BoujeeEnjinia1701/conepro/cad/drawings/CNP-DWG-001.pdf

CONCEPT, NOT FOR FABRICATION | ConePro · github.com/BoujeeEnjinia1701/conepro

FRONT VIEW
Scale 1:20; looking at the front (along +Y)

TOP VIEW
Scale 1:20; looking down (along -Z)

RIGHT VIEW
Scale 1:20; looking at the right side (along -X)

DETAIL A: ANVIL, SENSOR PAD AND CLAMP
Front view, scale 1:5

1,875 overall

713 = 138 + 575 drop

1,000 lower rod

939 stroke (850 usable)

300 plate

300

8 gap, pad to hammer face

105 rod to wire

100 hammer, 8.0 kg

ISOMETRIC VIEW
Not to scale; seen from the front right and above, about 30 deg elevation

MAIN DIMENSIONS AND INTERFACES (MM)
ASTM D6951: 8.0 kg hammer, 575 drop, 16 rod, 20 cone at 60 deg Hammer 100 OD x 22 bore x 138.0; anvil 64 x 60
Upper rod 778; stop collar 44 x 18; T-handle 260 wide
Plate 300 x 300 x 6 Al; 60 hole, 60 slot
Draw-wire exit at X 105, Y 40; 60 grooved drum, single layer
One-piece aluminum clamp, 40 collar against the anvil underside
M12 rod joints, no thread locker; spanner flats 17 A/F cone, 13 A/F rod, 55 A/F anvil Hammer: 3 grip grooves; 33 rubber grips on the T-handle
End cap 32 x 24 on the upper rod stud whenever it is off the anvil
Sensor pad on a band clamp (50 to 80 anvils), 8 below anvil top
Stroke 939, limited by the wire arm on reel housing
About 15.8 kg with bag; heaviest piece 9.96 kg (CNP-CAL-001 v0.6) Third-angle; front view from -Y; ground at Z 0
REV | DESCRIPTION | DATE | BY
P1 | Preliminary GA for TRL 3 (from cad/src/model.py) | 2026-09-25 | AC
P2 | 6 mm plate, aluminum clamp, 15.7 kg (CNP-DDR-002) | 2026-09-25 | AC
P3 | Reel housing 72 x 60 x 72 round the 60 mm drum; stroke 928 (CNP-DDR-003) | 2026-09-27 | AC
P4 | Layout and labels tidied | 2026-09-30 | AC
P5 | Design for construction: joints, clamp, reel, cables (CNP-DDR-004) | 2026-09-30 | AC
P6 | Spanner flats; hammer grooves; grips; end cap (2026-10-02) | 2026-10-02 | AC
CONEPRO | github.com/BoujeeEnjinia1701/conepro

## General arrangement

DRAWING NO.
CNP-DWG-001

REV
P6

SHEET
1 of 1

SIZE

## ANSI B

SCALE
1:20

UNITS
mm
PROJECTION | DATE
2026-10-02

DRAWN
Amish Chadha

MATERIAL / NOTES
Steel rods, anvil, hammer; aluminum plate and clamp; parts per bom/bom.csv. PRELIMINARY, NOT FOR FABRICATION
Licensed CERN-OHL-S-2.0 · Design Molecule Lab · designmolecule.com | Generated from cad/src; do not edit by hand
