BoujeeEnjinia1701/conepro/cad/drawings/CNP-DWG-101.pdf

### BUILD PLAN SKETCH, PLAN NOT YET BUILT ConePro · github.com/BoujeeEnjinia1701/conepro

FRONT VIEW
Scale 2:1; looking at the front (along +Y)

TOP VIEW
Scale 2:1; looking down (along -Z)

RIGHT VIEW
Scale 2:1; looking at the right side (along -X)

20

20 29

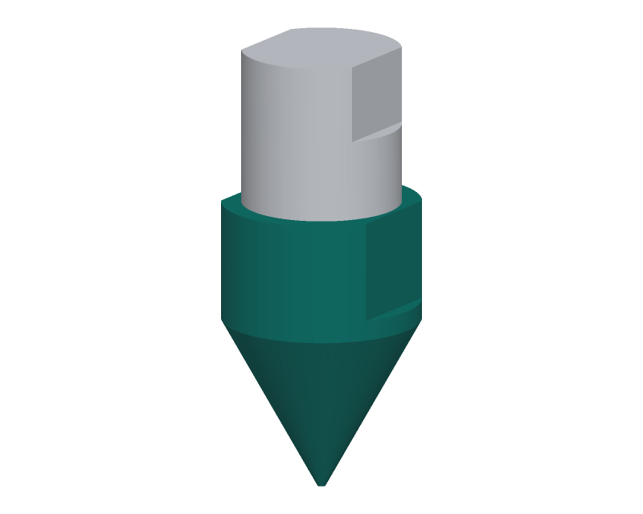
[picture p45: figure]

WHERE IT GOES
This part in colour, its neighbours in grey

HOW TO MAKE IT AND HOW IT FITS
Make two. Turn from 25 mm bar: a 20.0 mm diameter body 12 mm long with a 60 degree point below it (point 17.3 mm high), 29.3 mm overall. Keep the 20 mm diameter within 0.1 mm; a worn or undersize cone biases the DCP index. Leave a sharp point, no flat.
Top face: drill 10.2 mm 16 deep, tap M12 x 1.75 to 14 mm deep, and face it square to the axis: the rod shoulder bears on this face. Spanner flats: mill two flats 17 mm across on the top 10 mm of the body, leaving the bottom 2 mm and the 20 mm base edge round. Harden after tapping (about 50 HRC); run a tap through after. Fit: screws onto the M12 stud on the bottom of the lower rod with no thread locker; tighten with a 17 mm spanner on the cone and a 13 mm spanner on the rod flats until the shoulder seats. Check: 20.0 mm across the body; 60 degrees with a gauge; the rod shoulder sits flat on the top face with no gap.
REV | DESCRIPTION | DATE | BY
P1 | Making sketch for the prototype build plan | 2026-09-30 | AC
P2 | 17 mm spanner flats; no thread locker | 2026-10-02 | AC
CONEPRO | github.com/BoujeeEnjinia1701/conepro

## ConePro cone (make 2, one spare): making sketch

DRAWING NO.
CNP-DWG-101

REV
P2

SHEET
1 of 1

SIZE

## ANSI B

SCALE
2:1

UNITS
mm
PROJECTION | DATE
2026-10-02

DRAWN
Amish Chadha

MATERIAL / NOTES
Tool steel or 4140 round bar 25 mm, hardened after machining
Licensed CERN-OHL-S-2.0 · Design Molecule Lab · designmolecule.com | Generated from cad/src; do not edit by hand
