BoujeeEnjinia1701/conepro/cad/drawings/CNP-DWG-102.pdf

### BUILD PLAN SKETCH, PLAN NOT YET BUILT ConePro · github.com/BoujeeEnjinia1701/conepro

FRONT VIEW
Scale 1:2; looking at the front (along +Y)

TOP VIEW
Scale 1:2; looking down (along -Z)

RIGHT VIEW
Scale 1:2; looking at the right side (along -X)

Broken view: the middle of the rod is left out. True length 1,032 mm overall.

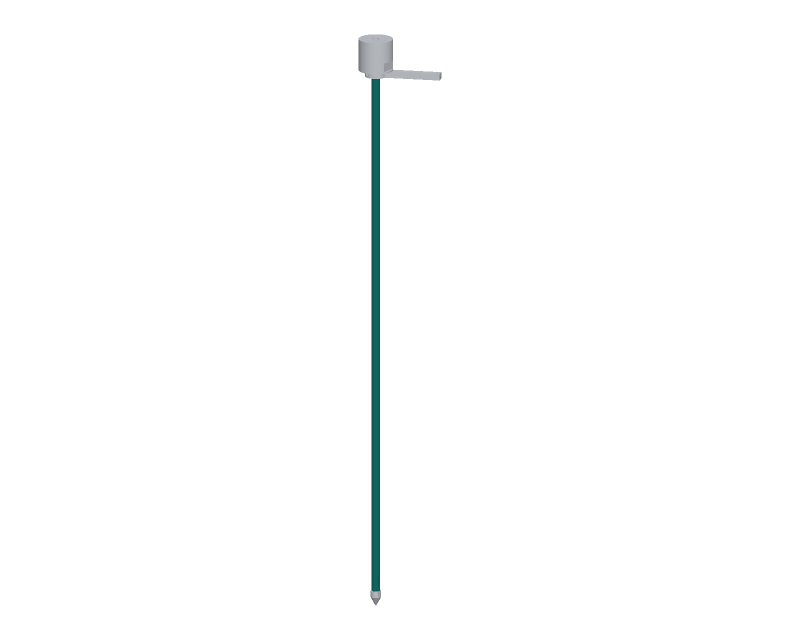
[picture p46: figure]

WHERE IT GOES
This part in colour, its neighbours in grey

HOW TO MAKE IT AND HOW IT FITS
Cut 1,032 mm of 16 mm rod; face both ends square.
Bottom end: turn an M12 x 1.75 stud 12 mm long (12.0 mm diameter) and cut the thread; leave a square, flat 16 mm shoulder.
Top end: turn an M12 stud 20 mm long the same way.
Spanner flats: mill two flats 13 mm across, 20 mm long, starting
8 mm above the bottom shoulder.
The shoulders are 1,000 mm apart. Both shoulders carry every
blow, so face them square and break the edge 0.5 mm.
Engrave a ring every 10 mm, deeper every 100 mm, measured up from the cone point with the cone fitted (the point is 29.3 mm
below the bottom shoulder). This is the backup depth scale.
Fit: the cone screws on the bottom stud, the anvil on the top
stud; the clamp collar slides on from the top before the anvil. Check: straight within 1 mm over its length when rolled on a flat bench; both studs take an M12 nut by hand.
REV | DESCRIPTION | DATE | BY
P1 | Making sketch for the prototype build plan | 2026-09-30 | AC
P2 | 13 mm spanner flats near the bottom shoulder | 2026-10-02 | AC
CONEPRO | github.com/BoujeeEnjinia1701/conepro

## ConePro lower drive rod: making sketch

DRAWING NO.
CNP-DWG-102

REV
P2

SHEET
1 of 1

SIZE

## ANSI B

SCALE
1:2

UNITS
mm
PROJECTION | DATE
2026-10-02

DRAWN
Amish Chadha

MATERIAL / NOTES
16 mm 4140 class steel rod, ground or bright
Licensed CERN-OHL-S-2.0 · Design Molecule Lab · designmolecule.com | Generated from cad/src; do not edit by hand
