BoujeeEnjinia1701/conepro/cad/drawings/CNP-DWG-103.pdf

### BUILD PLAN SKETCH, PLAN NOT YET BUILT ConePro · github.com/BoujeeEnjinia1701/conepro

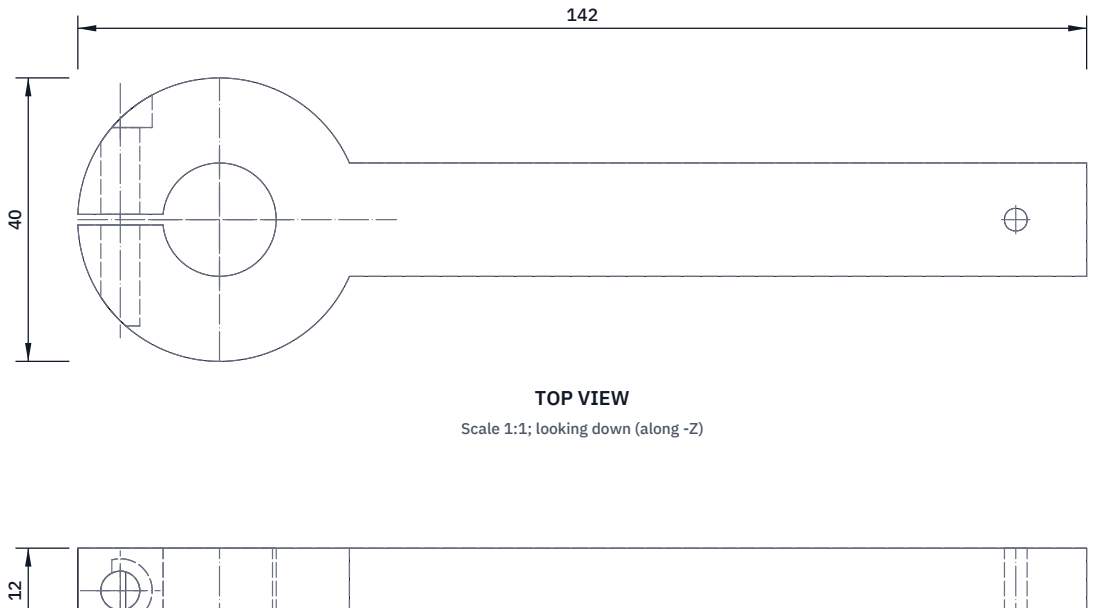
[picture p47: figure]
TOP VIEW; Scale 1:1; looking down (along -Z)

FRONT VIEW
Scale 1:1; looking at the front (along +Y)

RIGHT VIEW
Scale 1:1; looking at the right side (along -X)

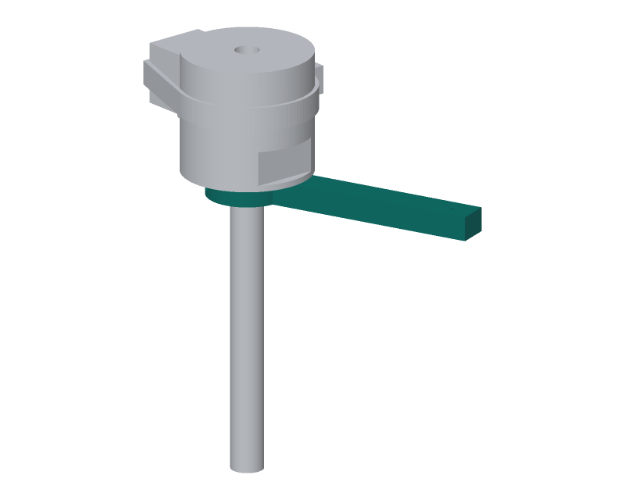
[picture p48: figure]

WHERE IT GOES
This part in colour, its neighbours in grey

HOW TO MAKE IT AND HOW IT FITS
One piece cut from 12 mm plate: a 40 mm round boss and an arm 16 mm wide reaching 122 mm from the boss centre.
Bore the boss 16 mm (a sliding fit on the rod, ream if you can). Wire eye: a 3.2 mm hole on the arm centre line, 112.4 mm from the bore centre; break both edges so the wire cannot chafe.
Saw a 1.5 mm slit from the bore out through the boss on the side opposite the arm.
Clamp screw: at 14 mm from the bore centre, square across the slit, drill 5.5 mm through the near jaw with a 9 mm spot face, and
drill 4.2 mm and tap M5 in the far jaw.
Fit: slides on the lower rod from the top; its top face butts the underside of the anvil, which carries it at every blow. Turn the arm to point at the reel's wire exit, then tighten the M5 screw. Check: slides on the rod with the screw slack; locks by hand.
REV | DESCRIPTION | DATE | BY
P1 | Making sketch for the prototype build plan | 2026-09-30 | AC
CONEPRO | github.com/BoujeeEnjinia1701/conepro

## ConePro clamp collar and wire arm: making sketch

DRAWING NO.
CNP-DWG-103

REV
P1

SHEET
1 of 1

SIZE

## ANSI B

SCALE
1:1

UNITS
mm
PROJECTION | DATE
2026-09-30

DRAWN
Amish Chadha

MATERIAL / NOTES
Aluminium plate 12 mm, 6061 class
Licensed CERN-OHL-S-2.0 · Design Molecule Lab · designmolecule.com | Generated from cad/src; do not edit by hand
