BoujeeEnjinia1701/conepro/cad/drawings/CNP-DWG-104.pdf

### BUILD PLAN SKETCH, PLAN NOT YET BUILT ConePro · github.com/BoujeeEnjinia1701/conepro

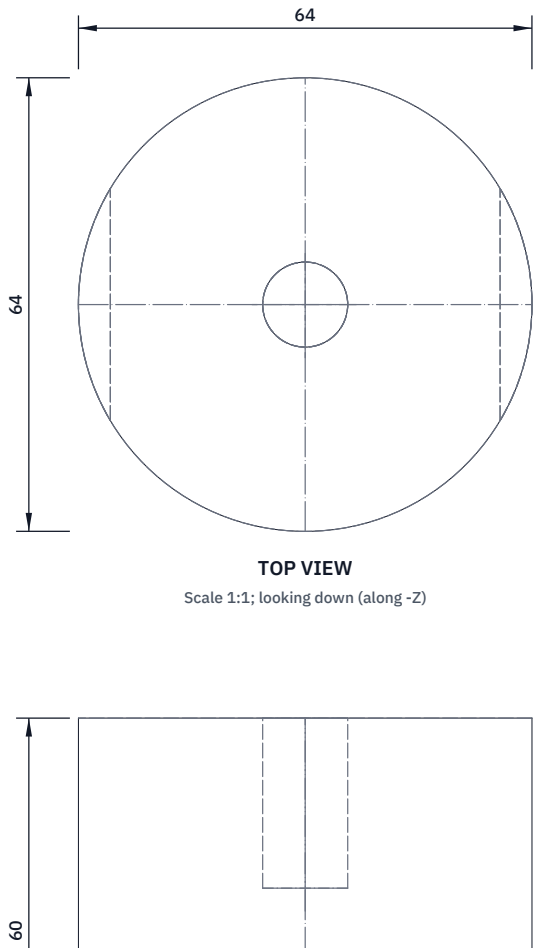
[picture p49: figure]
TOP VIEW; Scale 1:1; looking down (along -Z)

FRONT VIEW
Scale 1:1; looking at the front (along +Y)

RIGHT VIEW
Scale 1:1; looking at the right side (along -X)

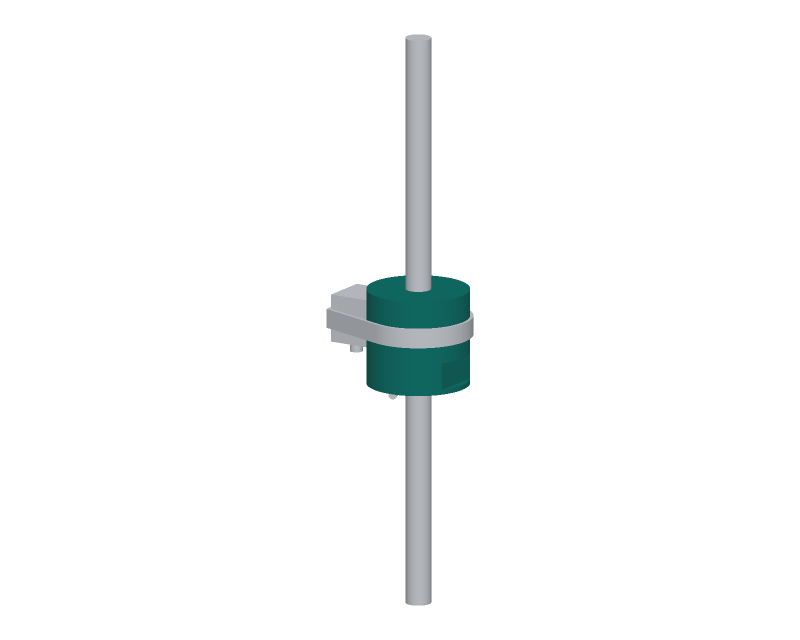
[picture p50: figure]

WHERE IT GOES
This part in colour, its neighbours in grey

HOW TO MAKE IT AND HOW IT FITS
Turn to 64 mm diameter x 60 mm long; face both ends square and parallel within 0.1 mm. Chamfer the outer edges 1 mm.
Both end faces: centre drill, drill 10.2 mm 27 mm deep and tap M12 x 1.75 to 24 mm deep. The two holes do not meet.
Spanner flats: mill two flats 55 mm across, 17 mm long, starting 3 mm above the bottom face, below the sensor pad.
The top face takes every hammer blow: leave it flat and smooth. Fit: both rod studs screw in to their shoulders with no thread locker, tightened with a 55 mm spanner on the anvil and the rod flats or T-handle. The clamp collar butts the bottom face; the sensor pad and band clamp onto its side.
Check: both rods seat on their shoulders with no rock; the anvil spins true on the rod within 0.2 mm.
REV | DESCRIPTION | DATE | BY
P1 | Making sketch for the prototype build plan | 2026-09-30 | AC
P2 | 55 mm spanner flats; no thread locker | 2026-10-02 | AC
CONEPRO | github.com/BoujeeEnjinia1701/conepro

## ConePro anvil: making sketch

DRAWING NO.
CNP-DWG-104

REV
P2

SHEET
1 of 1

SIZE

## ANSI B

SCALE
1:1

UNITS
mm
PROJECTION | DATE
2026-10-02

DRAWN
Amish Chadha

MATERIAL / NOTES
Steel round bar 70 mm, 1045 or 4140 class
Licensed CERN-OHL-S-2.0 · Design Molecule Lab · designmolecule.com | Generated from cad/src; do not edit by hand
