BoujeeEnjinia1701/conepro/cad/drawings/CNP-DWG-105.pdf

### BUILD PLAN SKETCH, PLAN NOT YET BUILT ConePro · github.com/BoujeeEnjinia1701/conepro

FRONT VIEW
Scale 1:2; looking at the front (along +Y)

TOP VIEW
Scale 1:2; looking down (along -Z)

RIGHT VIEW
Scale 1:2; looking at the right side (along -X)

100

100 138

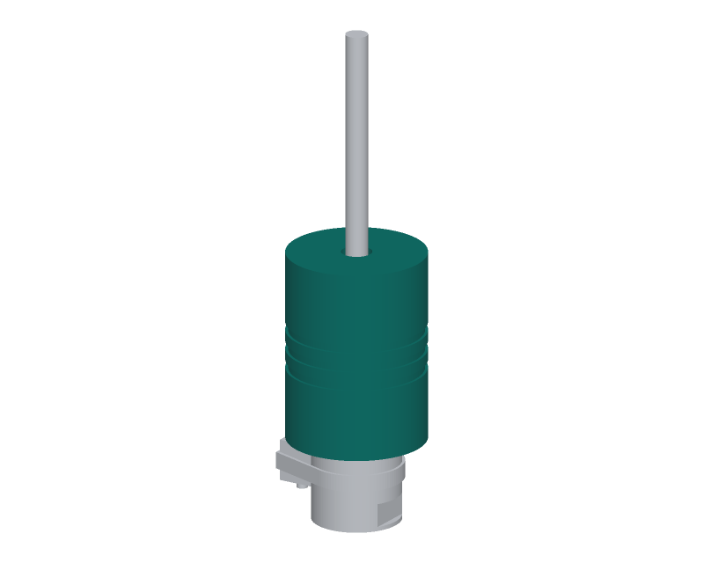
[picture p51: figure]

WHERE IT GOES
This part in colour, its neighbours in grey

HOW TO MAKE IT AND HOW IT FITS
Saw 140 mm of 100 mm bar. Bore 22 mm through.
Face both ends square; the lower face strikes the anvil.
Lower face: 16 pockets 8.2 mm diameter, 5 mm deep, equally spaced (22.5 degrees) on an 82 mm circle, all outside the 64 mm area
that strikes the anvil.
Grip grooves: turn 3 grooves 6 mm wide and 2 mm deep,
14 mm apart, centred on the middle of the length.
Weigh, then face the top end down to 8.00 kg, within 10 g.
The length is set at machining (about 138.0 mm).
Bond a 8 x 4 mm N42 magnet in each pocket with epoxy, 0.5 mm below the face, every one with the same pole facing down. Paint or oil the outside; keep the strike face bare. Stick the
"fit the end cap" label above the grooves.
Fit: slides on the upper rod (3 mm clearance all round) and falls 575 mm onto the anvil.
Check: 8.00 kg; slides freely the length of a 16 mm rod; no magnet stands proud of the face.
REV | DESCRIPTION | DATE | BY
P1 | Making sketch for the prototype build plan | 2026-09-30 | AC
P2 | Grip grooves; length set to keep 8.00 kg; label | 2026-10-02 | AC
CONEPRO | github.com/BoujeeEnjinia1701/conepro

## ConePro drop hammer: making sketch

DRAWING NO.
CNP-DWG-105

REV
P2

SHEET
1 of 1

SIZE

## ANSI B

SCALE
1:2

UNITS
mm
PROJECTION | DATE
2026-10-02

DRAWN
Amish Chadha

MATERIAL / NOTES
Steel round bar 100 mm, 1018 to 1045 class
Licensed CERN-OHL-S-2.0 · Design Molecule Lab · designmolecule.com | Generated from cad/src; do not edit by hand
