BoujeeEnjinia1701/conepro/cad/drawings/CNP-DWG-106.pdf

### BUILD PLAN SKETCH, PLAN NOT YET BUILT ConePro · github.com/BoujeeEnjinia1701/conepro

FRONT VIEW
Scale 1:2; looking at the front (along +Y)

TOP VIEW
Scale 1:2; looking down (along -Z)

RIGHT VIEW
Scale 1:2; looking at the right side (along -X)

Broken view: the middle of the rod is left out. True length 798 mm overall.

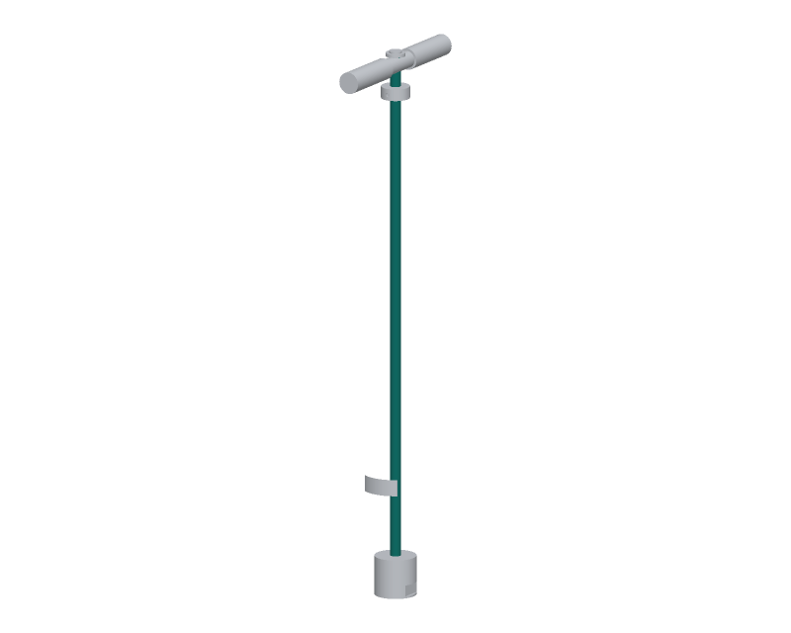
[picture p52: figure]

WHERE IT GOES
This part in colour, its neighbours in grey

HOW TO MAKE IT AND HOW IT FITS
Cut 798 mm of 16 mm rod; face both ends square.
Bottom end: turn an M12 x 1.75 stud 20 mm long with a square shoulder. The shoulder is the anvil top: measure from it.
The rod above the shoulder is 778.0 mm; its top end ends flush with the top of the T-handle tube.
Smooth the rod between the shoulder and 715 mm: the hammer slides on it.
The 6 mm roll pin hole, 722.0 mm above the shoulder, is drilled through the rod and the stop collar together (DWG-107).
Fit: the hammer goes on from the bottom end and the end cap screws on the stud; take it off to screw the stud into the
anvil with no thread locker, turned by the T-handle.
Check: straight within 0.5 mm; the hammer slides its whole length without sticking.
REV | DESCRIPTION | DATE | BY
P1 | Making sketch for the prototype build plan | 2026-09-30 | AC
P2 | Lengths for the grooved hammer; end cap; no thread locker | 2026-10-02 | AC
CONEPRO | github.com/BoujeeEnjinia1701/conepro

## ConePro upper rod (hammer guide): making sketch

DRAWING NO.
CNP-DWG-106

REV
P2

SHEET
1 of 1

SIZE

## ANSI B

SCALE
1:2

UNITS
mm
PROJECTION | DATE
2026-10-02

DRAWN
Amish Chadha

MATERIAL / NOTES
16 mm 4140 class steel rod, ground or bright
Licensed CERN-OHL-S-2.0 · Design Molecule Lab · designmolecule.com | Generated from cad/src; do not edit by hand
