BoujeeEnjinia1701/conepro/cad/drawings/CNP-DWG-107.pdf

### BUILD PLAN SKETCH, PLAN NOT YET BUILT ConePro · github.com/BoujeeEnjinia1701/conepro

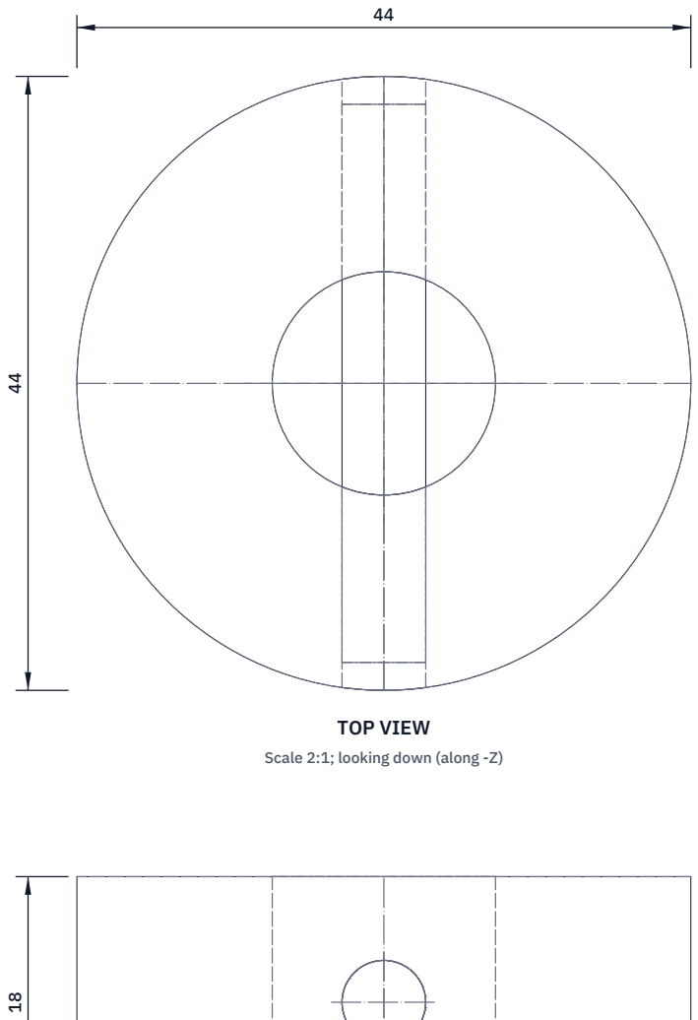
[picture p53: figure]
TOP VIEW; Scale 2:1; looking down (along -Z)

FRONT VIEW
Scale 2:1; looking at the front (along +Y)

RIGHT VIEW
Scale 2:1; looking at the right side (along -X)

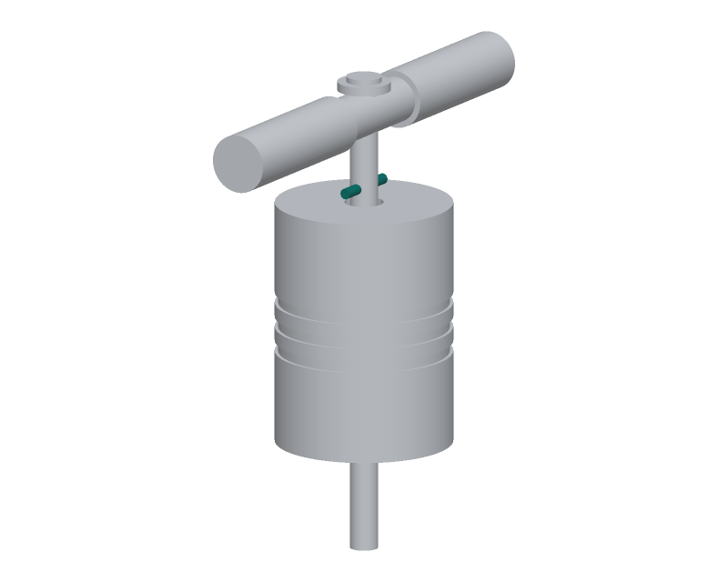
[picture p54: figure]

WHERE IT GOES
This part in colour, its neighbours in grey

HOW TO MAKE IT AND HOW IT FITS
Turn to 44 mm diameter x 18 mm; bore 16 mm, a close slide fit. Face both ends square; the hammer's top face hits the underside. Slide it on the upper rod from the top so its underside is
713.0 mm above the rod shoulder. With the 138.0 mm hammer this gives the 575 mm free drop. Set it with a rule and check
the drop with the hammer on a flat plate standing for the anvil. Clamp it there and drill 6 mm straight through collar and rod together, at mid-height (722.0 mm above the shoulder).
Drive in a 6 x 40 mm spring steel roll pin; its ends sit just
inside the collar's outside surface.
Check: the free drop is 575 mm, within 2 mm; the collar does not move when the hammer is jerked up against it.
REV | DESCRIPTION | DATE | BY
P1 | Making sketch for the prototype build plan | 2026-09-30 | AC
P2 | Heights for the grooved hammer | 2026-10-02 | AC
CONEPRO | github.com/BoujeeEnjinia1701/conepro

## ConePro top stop collar: making sketch

DRAWING NO.
CNP-DWG-107

REV
P2

SHEET
1 of 1

SIZE

## ANSI B

SCALE
2:1

UNITS
mm
PROJECTION | DATE
2026-10-02

DRAWN
Amish Chadha

MATERIAL / NOTES
Steel round bar 50 mm, 1018 class
Licensed CERN-OHL-S-2.0 · Design Molecule Lab · designmolecule.com | Generated from cad/src; do not edit by hand
