BoujeeEnjinia1701/conepro/cad/drawings/CNP-DWG-108.pdf

### BUILD PLAN SKETCH, PLAN NOT YET BUILT ConePro · github.com/BoujeeEnjinia1701/conepro

FRONT VIEW
Scale 1:2; looking at the front (along +Y)

TOP VIEW
Scale 1:2; looking down (along -Z)

RIGHT VIEW
Scale 1:2; looking at the right side (along -X)

266

33 38

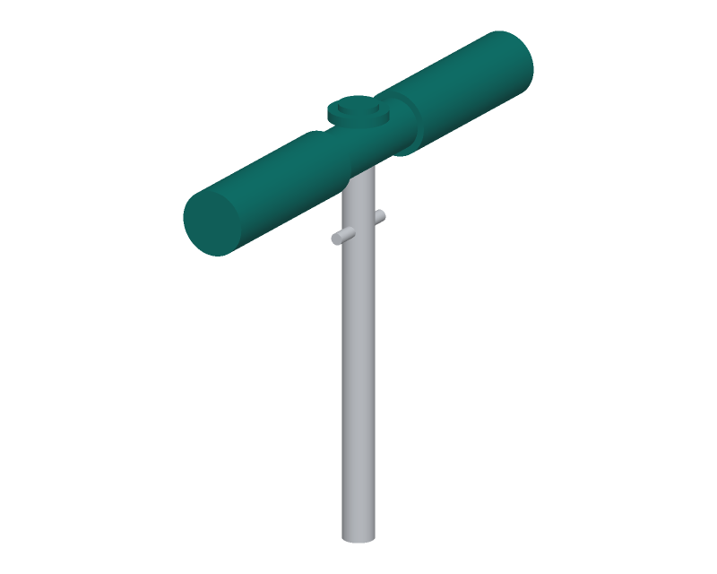
[picture p55: figure]

WHERE IT GOES
This part in colour, its neighbours in grey

HOW TO MAKE IT AND HOW IT FITS
Tube: cut 260 mm of 26 x 2.5 mm steel tube; deburr.
At mid-length drill 16 mm straight through both walls, square to the tube, so the upper rod passes through.
Seat disc: 30 mm diameter, 5 mm thick, with a 20 mm recess 3 mm deep in its top face.
Fit: push the upper rod up through the tube until its top end is flush with the top of the tube, the tube square to the rod.
Weld the tube to the rod all round where the rod comes out, top and bottom (or have a shop do it). Weld the disc centred on the rod top. Paint, then bond the 20 mm bubble level in the recess. Grips: push a closed-end rubber grip, about 33 mm across and 100 mm long, over each tube end (soapy water helps).
Check: the level reads centred when the rod hangs plumb; the handle is square to the rod within 1 degree.
REV | DESCRIPTION | DATE | BY
P1 | Making sketch for the prototype build plan | 2026-09-30 | AC
P2 | Rubber grips on the tube ends | 2026-10-02 | AC
CONEPRO | github.com/BoujeeEnjinia1701/conepro

## ConePro T-handle, level seat and level: making sketch

DRAWING NO.
CNP-DWG-108

REV
P2

SHEET
1 of 1

SIZE

## ANSI B

SCALE
1:2

UNITS
mm
PROJECTION | DATE
2026-10-02

DRAWN
Amish Chadha

MATERIAL / NOTES
Steel tube 26 x 2.5 mm; steel disc 30 x 5 mm; bought bullseye level
Licensed CERN-OHL-S-2.0 · Design Molecule Lab · designmolecule.com | Generated from cad/src; do not edit by hand
