BoujeeEnjinia1701/conepro/cad/drawings/CNP-DWG-109.pdf

### BUILD PLAN SKETCH, PLAN NOT YET BUILT ConePro · github.com/BoujeeEnjinia1701/conepro

FRONT VIEW
Scale 1:1; looking at the front (along +Y)

TOP VIEW
Scale 1:1; looking down (along -Z)

RIGHT VIEW
Scale 1:1; looking at the right side (along -X)

21

30 38

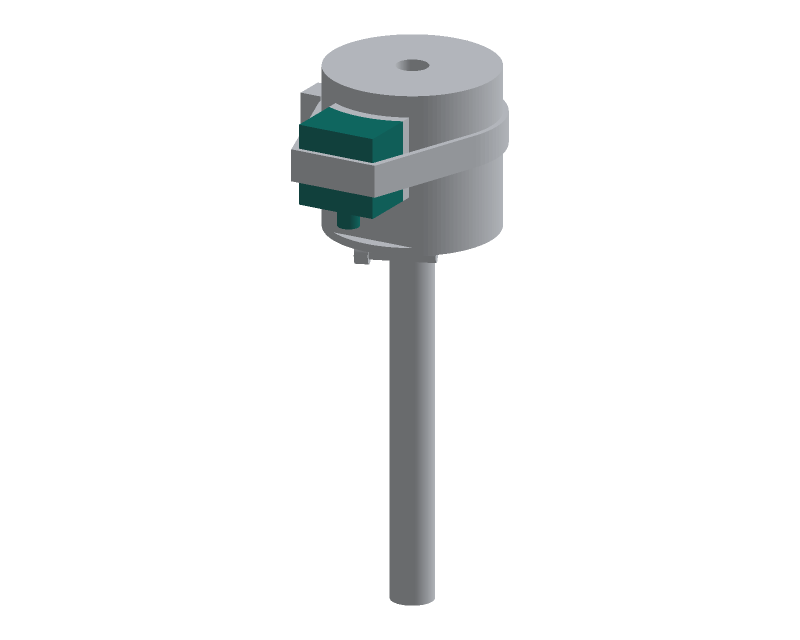
[picture p56: figure]

WHERE IT GOES
This part in colour, its neighbours in grey

HOW TO MAKE IT AND HOW IT FITS
Shell: print 30 wide x 30 tall x 18 deep at the middle, open at the back, 2 mm walls. The face toward the anvil is curved to a 36 mm radius (anvil radius plus the 4 mm isolator).
For another anvil size use its radius plus 4 mm.
Fit the sensor board (Hall switch and accelerometer) with the Hall switch 1 mm under the top face; feed the cable through the 6 mm hole in the boss under the pad.
Fill with potting epoxy; let it cure fully before use.
Isolator: cut 30 x 30 mm of 4 mm elastomer; it bends to the anvil. Bond it to the pad's curved face.
Fit: the pad sits on the anvil side, its top 8 mm below the anvil top, under the hammer's overhang. The band clamp goes round the anvil and over the pad's outer face.
Check: the pad is fully potted; no wire shows at the top.
REV | DESCRIPTION | DATE | BY
P1 | Making sketch for the prototype build plan | 2026-09-30 | AC
CONEPRO | github.com/BoujeeEnjinia1701/conepro

## ConePro blow and tilt sensor pad: making sketch

DRAWING NO.
CNP-DWG-109

REV
P1

SHEET
1 of 1

SIZE

## ANSI B

SCALE
1:1

UNITS
mm
PROJECTION | DATE
2026-09-30

DRAWN
Amish Chadha

MATERIAL / NOTES
Printed PETG or ASA shell, potting epoxy; 4 mm elastomer sheet
Licensed CERN-OHL-S-2.0 · Design Molecule Lab · designmolecule.com | Generated from cad/src; do not edit by hand
