BoujeeEnjinia1701/conepro/cad/drawings/CNP-DWG-110.pdf

### BUILD PLAN SKETCH, PLAN NOT YET BUILT ConePro · github.com/BoujeeEnjinia1701/conepro

FRONT VIEW
Scale 1:5; looking at the front (along +Y)

TOP VIEW
Scale 1:5; looking down (along -Z)

RIGHT VIEW
Scale 1:5; looking at the right side (along -X)

300

300 6

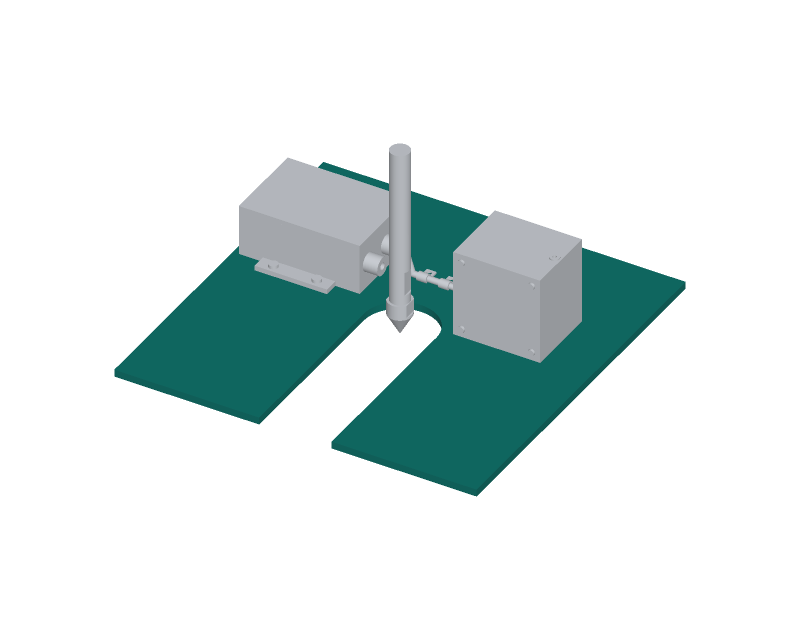
[picture p57: figure]

WHERE IT GOES
This part in colour, its neighbours in grey

HOW TO MAKE IT AND HOW IT FITS
Cut a 300 x 300 mm blank; round the corners 10 mm; deburr. Positions from the plate centre: X toward the reel side, Y away from the slot. The hole positions picture repeats them.
Centre hole 60 mm; a 60 mm wide slot from the hole to the -Y edge (chain drill, jigsaw, file straight).
Reel: four 4.2 mm holes, countersunk from below for M4, at X 45.3 and 103.3, Y 30 and 60.
Logger flanges: four holes drilled 3.3 mm and tapped M4 at X -113 and -77, Y 14 and 96.
P-clips: two holes tapped M4 at (X 4, Y 66) and (X -14, Y 66). Check: lies flat on a bench within 1 mm; screw heads under the plate sit flush or below the bottom face.
REV | DESCRIPTION | DATE | BY
P1 | Making sketch for the prototype build plan | 2026-09-30 | AC
CONEPRO | github.com/BoujeeEnjinia1701/conepro

## ConePro reference plate: making sketch

DRAWING NO.
CNP-DWG-110

REV
P1

SHEET
1 of 1

SIZE

## ANSI B

SCALE
1:5

UNITS
mm
PROJECTION | DATE
2026-09-30

DRAWN
Amish Chadha

MATERIAL / NOTES
Aluminium plate 6 mm, 5083 or 6082 class
Licensed CERN-OHL-S-2.0 · Design Molecule Lab · designmolecule.com | Generated from cad/src; do not edit by hand
