BoujeeEnjinia1701/conepro/cad/drawings/CNP-DWG-111.pdf

### BUILD PLAN SKETCH, PLAN NOT YET BUILT ConePro · github.com/BoujeeEnjinia1701/conepro

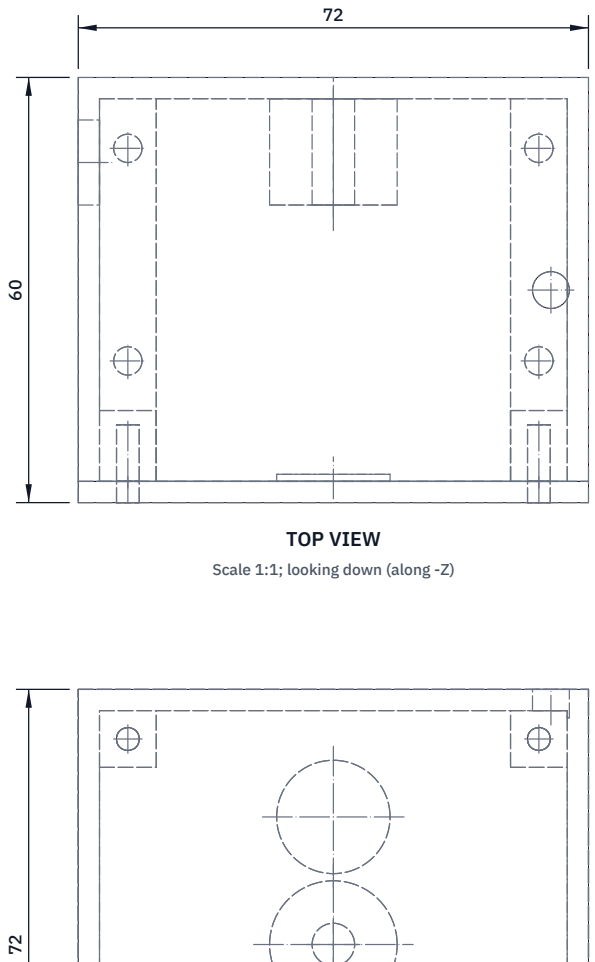
[picture p58: figure]
TOP VIEW; Scale 1:1; looking down (along -Z)
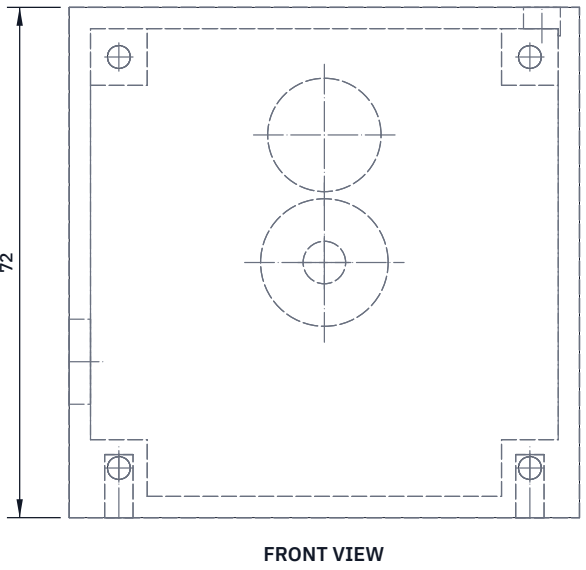
[picture p59: figure]
FRONT VIEW

Scale 1:1; looking at the front (along +Y)

RIGHT VIEW
Scale 1:1; looking at the right side (along -X)

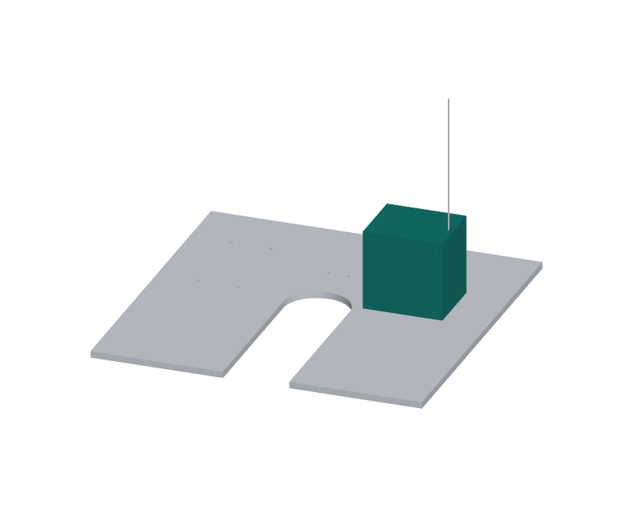
[picture p60: figure]

WHERE IT GOES
This part in colour, its neighbours in grey

HOW TO MAKE IT AND HOW IT FITS
Body: 72 wide x 57 deep x 72 tall outside, 3 mm walls, open on the front (-Y) face. Print standing on its base.
Inside, four 8 x 8 mm posts at the corners: the lower two run front to back, the upper two are 10 mm long at the front.
Bearing boss on the back wall, 18 mm diameter x 15 mm, centred 36 mm from the left face and 36 mm up: press in two 6 x 13 x 5 mm bearings.
Top: a 5.2 mm hole for the wire eyelet, 5.3 mm in from the right face and on the front-to-back centre line.
Left face: a 12 mm hole for the cable gland, 12 mm from the back and 22 mm up.
Inserts: M4 into the lower posts from below (two per post, 20 and 50 mm from the front); M3 into the four post ends at the front. Lid: 72 x 72 x 3 mm, four 3.4 mm holes over the post ends, and a pad for the sensor board. Seal with a 1.5 mm cord in the joint.
REV | DESCRIPTION | DATE | BY
P1 | Making sketch for the prototype build plan | 2026-09-30 | AC
CONEPRO | github.com/BoujeeEnjinia1701/conepro

## ConePro draw-wire reel housing and lid: making sketch

DRAWING NO.
CNP-DWG-111

REV
P1

SHEET
1 of 1

SIZE

## ANSI B

SCALE
1:1

UNITS
mm
PROJECTION | DATE
2026-09-30

DRAWN
Amish Chadha

MATERIAL / NOTES
Printed ASA or PETG, 100 % infill walls; brass heat-set inserts
Licensed CERN-OHL-S-2.0 · Design Molecule Lab · designmolecule.com | Generated from cad/src; do not edit by hand
