BoujeeEnjinia1701/conepro/cad/drawings/CNP-DWG-112.pdf

### BUILD PLAN SKETCH, PLAN NOT YET BUILT ConePro · github.com/BoujeeEnjinia1701/conepro

FRONT VIEW
Scale 1:1; looking at the front (along +Y)

TOP VIEW
Scale 1:1; looking down (along -Z)

RIGHT VIEW
Scale 1:1; looking at the right side (along -X)

60

20 60

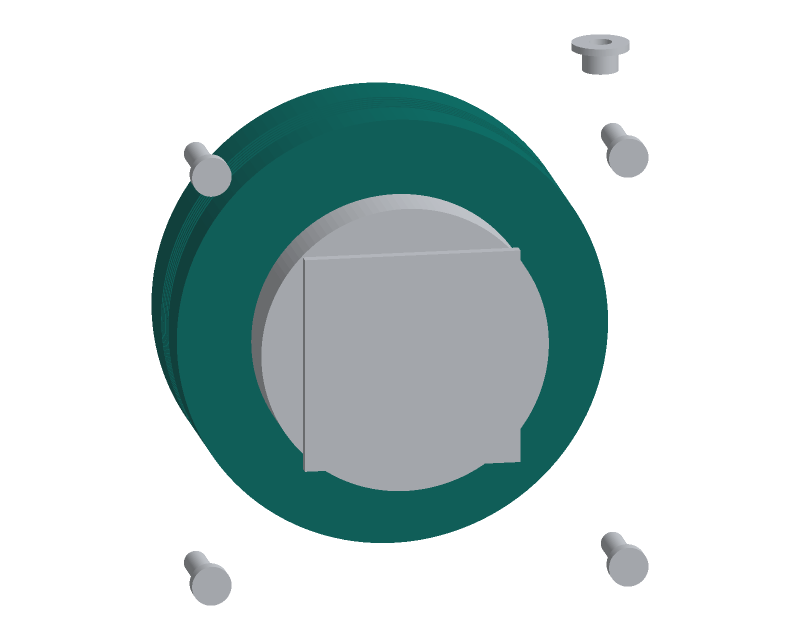
[picture p61: figure]

WHERE IT GOES
This part in colour, its neighbours in grey

HOW TO MAKE IT AND HOW IT FITS
Turn to 60.0 mm diameter x 20 mm; bore 6 mm (a close fit on the shaft). The diameter sets the scale: 188.5 mm of wire per turn. Cut a helical groove 1 mm pitch and 0.5 mm deep over 7 mm of the width, centred, with the lathe set to screw-cut 1 mm pitch. Drill a 1 mm anchor hole at the start of the groove for the
wire end, and an M3 set screw hole into the bore.
Fit: on the 6 mm shaft beside the spring motor, set screw on the shaft flat. The wire leaves the drum straight up under the eyelet: the drum's right-hand edge is under the eyelet. Wind the 1,000 mm wire on in a single layer, in the groove. Check: runs true within 0.05 mm; the wire lies in the groove in one layer with the arm at the full 939 mm stroke.
REV | DESCRIPTION | DATE | BY
P1 | Making sketch for the prototype build plan | 2026-09-30 | AC
CONEPRO | github.com/BoujeeEnjinia1701/conepro

## ConePro draw-wire drum: making sketch

DRAWING NO.
CNP-DWG-112

REV
P1

SHEET
1 of 1

SIZE

## ANSI B

SCALE
1:1

UNITS
mm
PROJECTION | DATE
2026-09-30

DRAWN
Amish Chadha

MATERIAL / NOTES
Aluminium round bar 65 mm, 6061 class
Licensed CERN-OHL-S-2.0 · Design Molecule Lab · designmolecule.com | Generated from cad/src; do not edit by hand
