BoujeeEnjinia1701/conepro/cad/drawings/CNP-DWG-113.pdf

### BUILD PLAN SKETCH, PLAN NOT YET BUILT ConePro · github.com/BoujeeEnjinia1701/conepro

FRONT VIEW
Scale 1:2; looking at the front (along +Y)

TOP VIEW
Scale 1:2; looking down (along -Z)

RIGHT VIEW
Scale 1:2; looking at the right side (along -X)

100

94 42

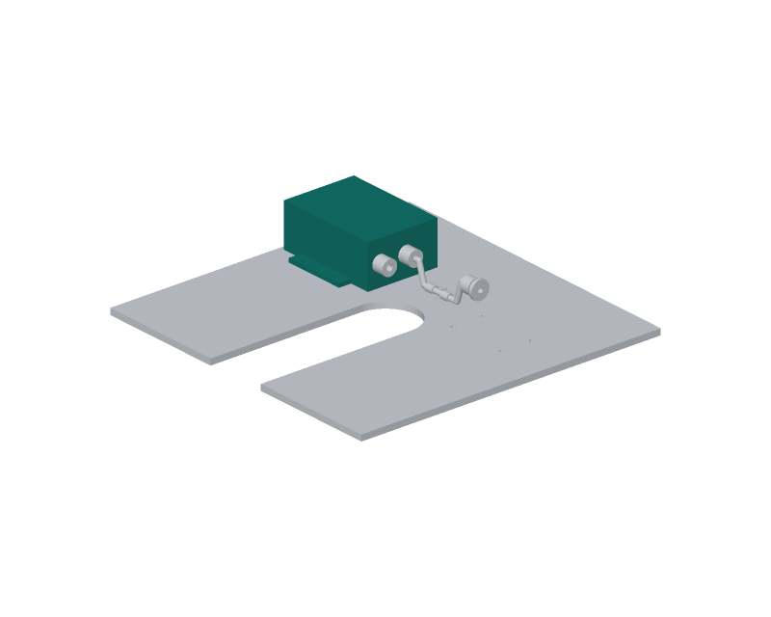
[picture p62: figure]

WHERE IT GOES
This part in colour, its neighbours in grey

HOW TO MAKE IT AND HOW IT FITS
Buy a flanged IP65 box about 100 x 70 x 42 mm with a gasketed lid; its flange holes go 82 mm apart across the box and 36 mm apart along it (or move the plate holes to suit your box).
Drill two 12 mm holes in the end wall that faces the rod, both
21 mm above the box floor's underside: one 12 mm and one 38 mm from the box side nearest the plate slot.
The first takes the M12 gland for the coiled sensor cable, the second the gland for the reel cable.
Pilot drill 3 mm, open with a step drill at low speed, deburr. Inside: the three-AA holder on the floor at the far end, the logger board near the glands, on double-sided foam tape or the box's own bosses.
Fit: flanges flat on the plate, four M4 pan-head screws into the tapped plate holes.
Check: the lid gasket seats all round; both glands tighten on their cables.
REV | DESCRIPTION | DATE | BY
P1 | Making sketch for the prototype build plan | 2026-09-30 | AC
CONEPRO | github.com/BoujeeEnjinia1701/conepro

## ConePro logger box: drilling sketch

DRAWING NO.
CNP-DWG-113

REV
P1

SHEET
1 of 1

SIZE

## ANSI B

SCALE
1:2

UNITS
mm
PROJECTION | DATE
2026-09-30

DRAWN
Amish Chadha

MATERIAL / NOTES
Bought IP65 ABS or polycarbonate box with flanges
Licensed CERN-OHL-S-2.0 · Design Molecule Lab · designmolecule.com | Generated from cad/src; do not edit by hand
