BoujeeEnjinia1701/conepro/cad/drawings/CNP-DWG-001.png

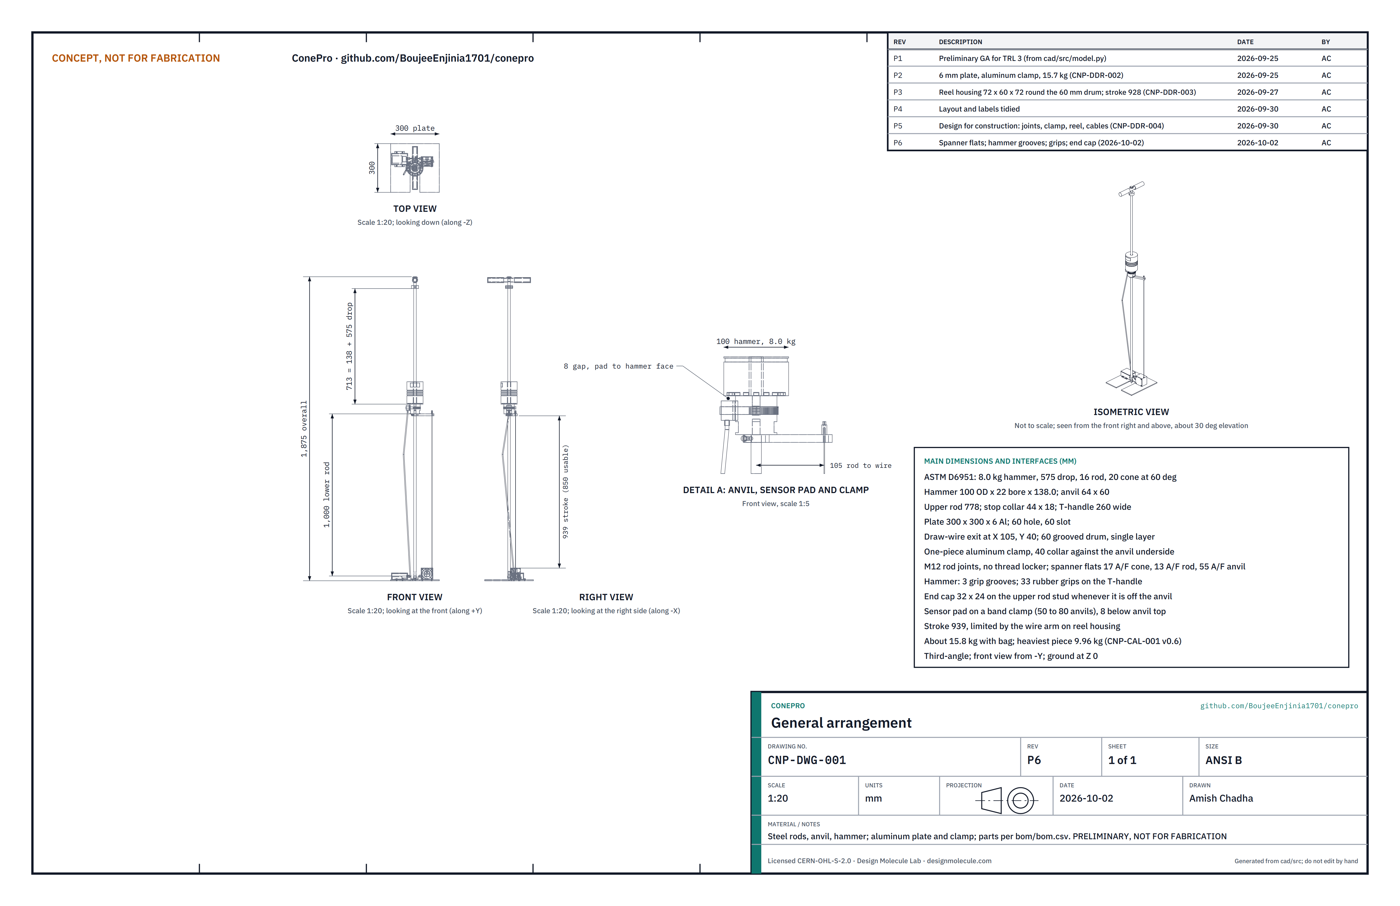
cad/drawings/CNP-DWG-001.png
