BoujeeEnjinia1701/conepro/media/card.png

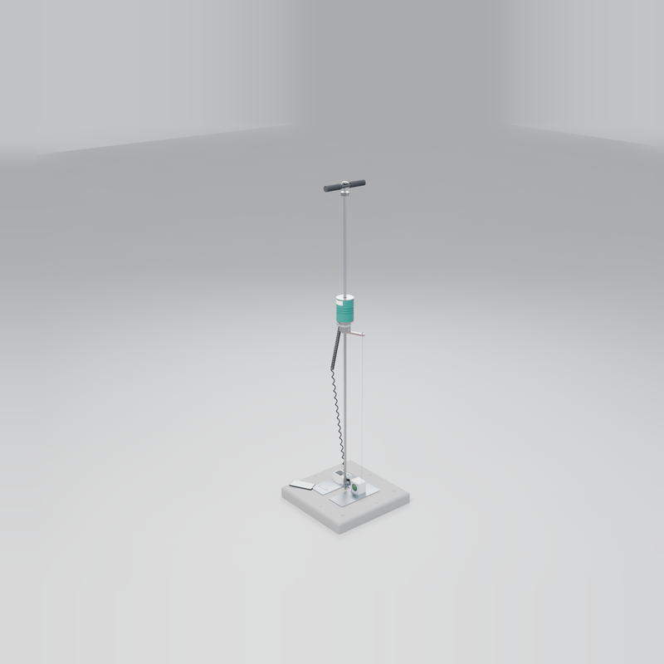
media/card.png
