BoujeeEnjinia1701/conepro/media/render-detail.png

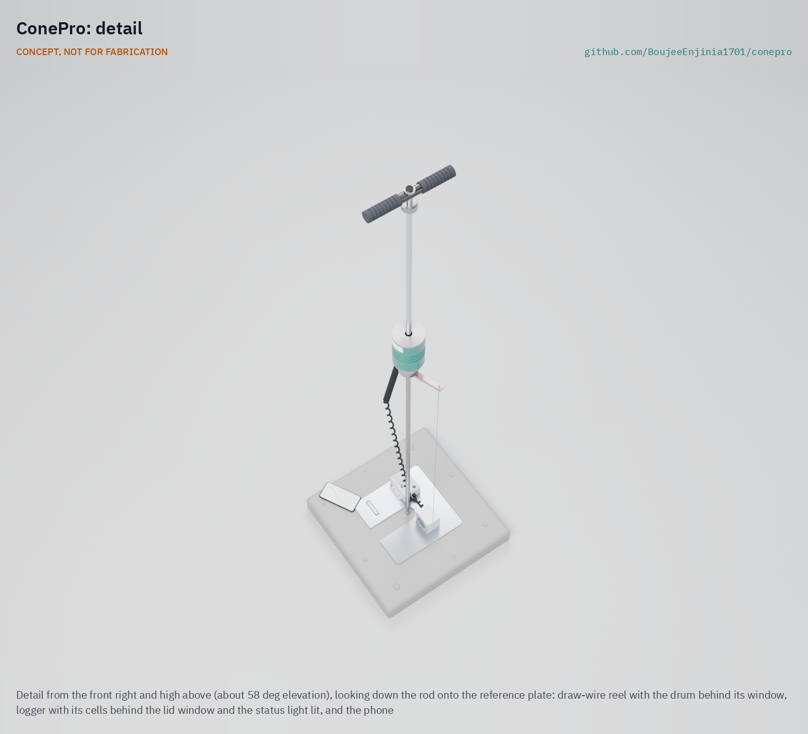
media/render-detail.png
