BoujeeEnjinia1701/conepro/media/render-exploded.png

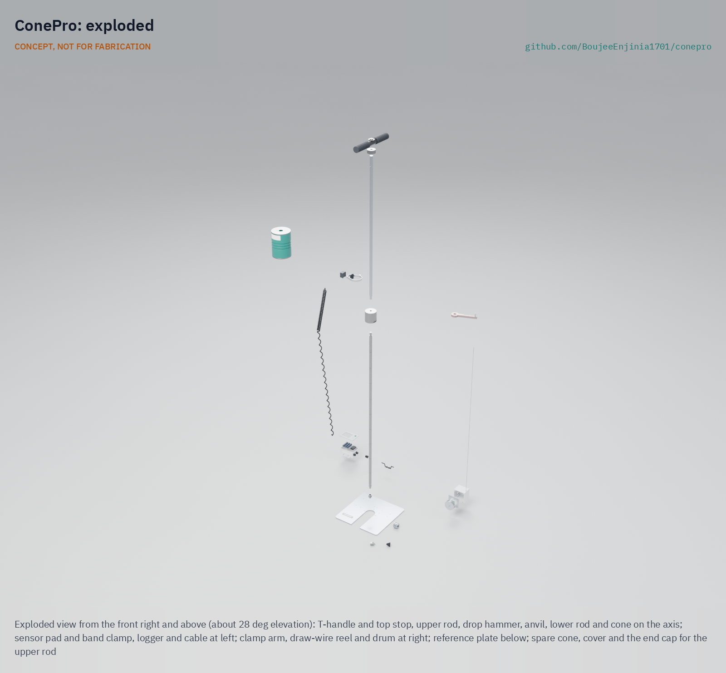
media/render-exploded.png
