BoujeeEnjinia1701/conepro/media/social-preview.png

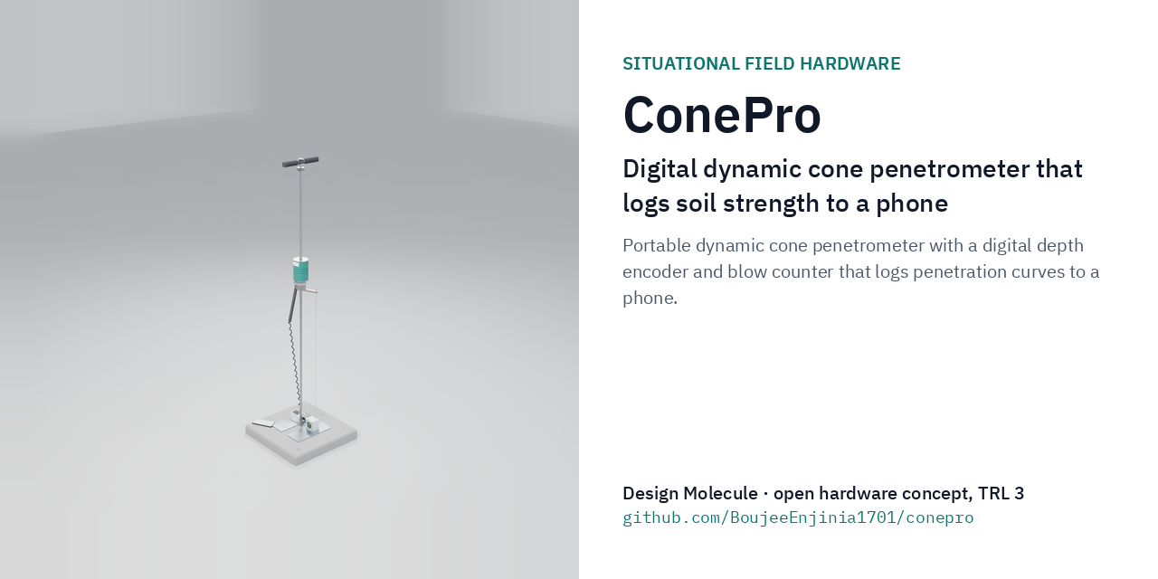
media/social-preview.png
